rbaron/w-parasite/assets/photos/original/plant1.jpg

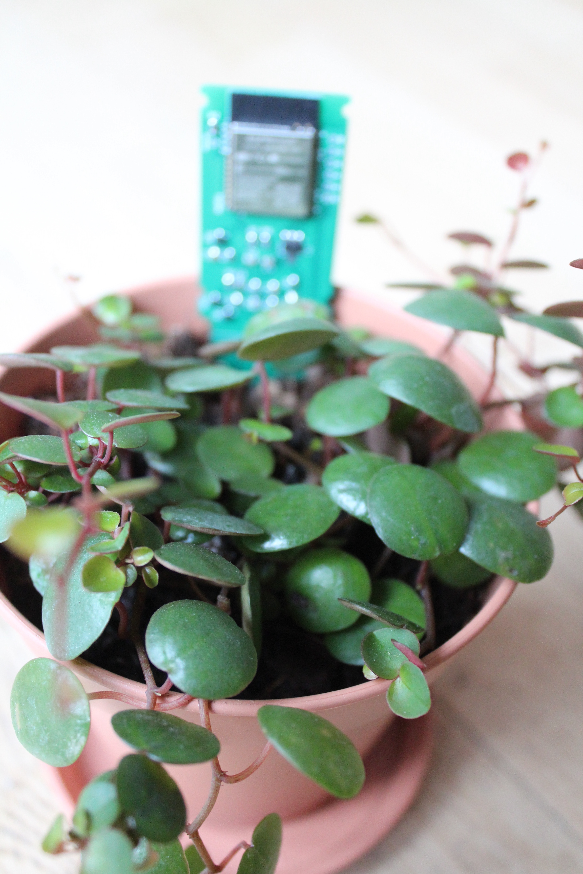
assets/photos/original/plant1.jpg
