rbaron/w-parasite/assets/photos/original/plant2.jpg

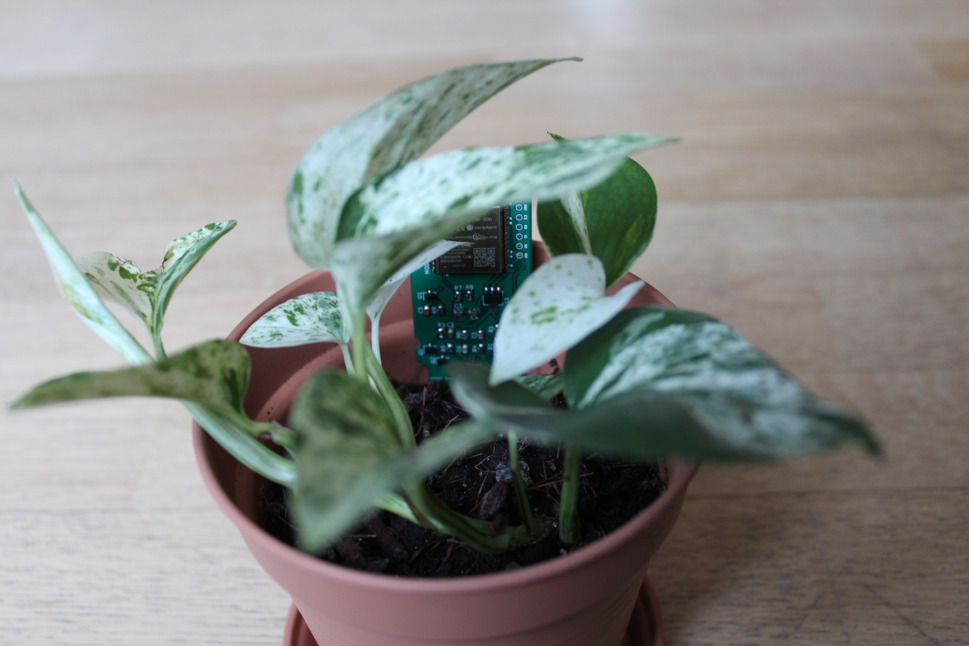
assets/photos/original/plant2.jpg
